jeffkub/wifi-hydrometer/firmware/wifi-hydrometer/src/si1145.cpp

#include "si1145.h"

#include <Wire.h>

void SI1145::write8(uint8_t reg, uint8_t value)
{
    Wire.beginTransmission(_i2caddr);
    Wire.write(reg);
    Wire.write(value);
    Wire.endTransmission();

    return;
}

uint8_t SI1145::read8(uint8_t reg)
{
    Wire.beginTransmission(_i2caddr);
    Wire.write(reg);
    Wire.endTransmission();

    Wire.requestFrom(_i2caddr, (uint8_t)1);
    return Wire.read();
}

uint16_t SI1145::read16(uint8_t reg)
{
    uint16_t value;

    Wire.beginTransmission(_i2caddr);
    Wire.write(reg);
    Wire.endTransmission();

    Wire.requestFrom(_i2caddr, (uint8_t)2);
    value = Wire.read();
    value |= (uint16_t)Wire.read() << 8;

    return value;
}

uint8_t SI1145::writeParam(uint8_t param, uint8_t value)
{
    write8(SI1145_PARAM_WR, value);
    write8(SI1145_COMMAND, SI1145_COMMAND_PARAM_SET | param);
    return read8(SI1145_PARAM_RD);
}

uint8_t SI1145::readParam(uint8_t param)
{
    write8(SI1145_COMMAND, SI1145_COMMAND_PARAM_QUERY | param);
    return read8(SI1145_PARAM_RD);
}

int SI1145::command(uint8_t cmd)
{
    uint8_t resp;
    unsigned int retry;

    /* Clear the response register */
    write8(SI1145_COMMAND, SI1145_COMMAND_NOP);
    resp = read8(SI1145_RESPONSE);
    if(resp)
    {
        return -1;
    }

    /* Write the command */
    write8(SI1145_COMMAND, cmd);

    /* Wait for response */
    for(retry = 0; retry < 25; retry++)
    {
        delay(1);

        resp = read8(SI1145_RESPONSE);
        if(resp & 0xF0)
        {
            /* An error has ocurred */
            return -1;
        }
        else if(resp)
        {
            /* Success */
            return 0;
        }
    }

    /* Timeout */
    return -1;
}

SI1145::SI1145(uint8_t addr) :
    _i2caddr(addr)
{
    return;
}

bool SI1145::begin(void)
{
    uint8_t part_id;

    /* Check connection */
    part_id = read8(SI1145_PART_ID);
    if(part_id != SI1145_PART_ID_SI1145)
    {
        return false;
    }

    /* Reset device */
    write8(SI1145_COMMAND, SI1145_COMMAND_RESET);
    delay(10);

    /* Write HW key for proper operation */
    write8(SI1145_HW_KEY, SI1145_HW_KEY_VAL);

    /* Enable UV index measurement coefficients */
    write8(SI1145_UCOEF0, 0x29);
    write8(SI1145_UCOEF1, 0x89);
    write8(SI1145_UCOEF2, 0x02);
    write8(SI1145_UCOEF3, 0x00);

    /* Enable UV sensor */
    writeParam(SI1145_PARAM_CHLIST,
        SI1145_PARAM_CHLIST_EN_UV |
        SI1145_PARAM_CHLIST_EN_ALS_IR |
        SI1145_PARAM_CHLIST_EN_ALS_VIS);

    /* Ambient light sensor params */
    writeParam(SI1145_PARAM_ALS_IR_ADCMUX, SI1145_PARAM_ALS_IR_ADCMUX_SMALLIR);
    writeParam(SI1145_PARAM_ALS_IR_ADC_COUNTER, SI1145_PARAM_ALS_ADC_COUNTER_511);
    writeParam(SI1145_PARAM_ALS_IR_ADC_GAIN, SI1145_PARAM_ALS_ADC_GAIN_DIV1);
    writeParam(SI1145_PARAM_ALS_IR_ADC_MISC, SI1145_PARAM_ALS_ADC_MISC_HIRANGE);

    writeParam(SI1145_PARAM_ALS_VIS_ADC_COUNTER, SI1145_PARAM_ALS_ADC_COUNTER_511);
    writeParam(SI1145_PARAM_ALS_VIS_ADC_GAIN, SI1145_PARAM_ALS_ADC_GAIN_DIV1);
    writeParam(SI1145_PARAM_ALS_VIS_ADC_MISC, SI1145_PARAM_ALS_ADC_MISC_HIRANGE);

    return true;
}

void SI1145::wake(void)
{
    /* Nothing to do */
    return;
}

void SI1145::shutdown(void)
{
    /* Nothing to do */
    return;
}

void SI1145::read(void)
{
    /* Force measurement */
    if(command(SI1145_COMMAND_ALS_FORCE))
    {
        return;
    }

    /* Read measurement results */
    vis = (float)read16(SI1145_ALS_VIS_DATA0) /  0.282f / 14.5f;
    ir = (float)read16(SI1145_ALS_IR_DATA0) /  2.44f / 14.5f;
    uv = (float)read16(SI1145_AUX_DATA0) / 100.0f;

    return;
}
